diazjacob/COMP-4300-Project/Schematics/Pico_Sensor_Array/Pico_Sensor_Array.kicad_sch

## KiCad design Schematics/Pico_Sensor_Array/Pico_Sensor_Array.kicad_sch (2022-12-15, an earlier design)

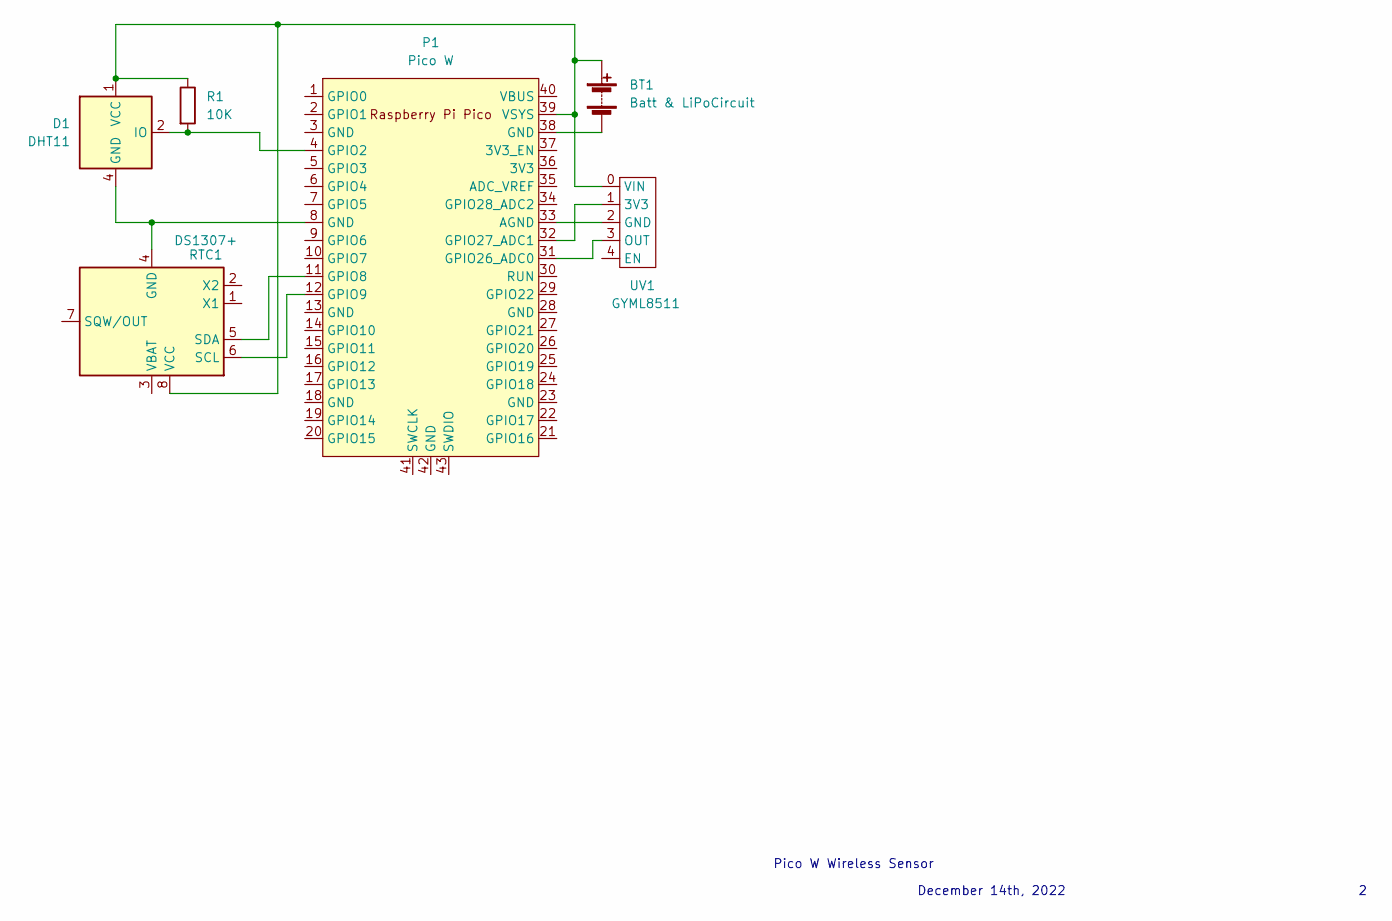
[picture p18: schematic Pico_Sensor_Array.kicad_sch]

Parts:
BT1: Batt & LiPoCircuit
D1: DHT11; Aosong_DHT11_5.5x12.0_P2.54mm
P1: Pico W; RPi_Pico_SMD_TH
R1: 10K
RTC1: DS1307+; DIP-8_W7.62mm
UV1: GYML8511

Connections:
unnamed: BT1.1 (+), D1.1 (VCC), P1.39 (VSYS), R1.1, RTC1.8 (VCC), UV1.0 (VIN)
unnamed: BT1.2 (-), P1.38 (GND)
unnamed: D1.2 (IO), P1.4 (GPIO2), R1.2
unnamed: D1.4 (GND), P1.8 (GND), RTC1.4 (GND)
unnamed: P1.11 (GPIO8), RTC1.5 (SDA)
unnamed: P1.12 (GPIO9), RTC1.6 (SCL)
unnamed: P1.31 (GPIO26_ADC0), UV1.3 (OUT)
unnamed: P1.32 (GPIO27_ADC1), UV1.1 (3V3)
unnamed: P1.33 (AGND), UV1.2 (GND)

Notes on the sheet:
December 14th, 2022
Pico W Wireless Sensor
